EmpiricalEE/uUSB-FP/output/BP1_3D_v240915.jpg

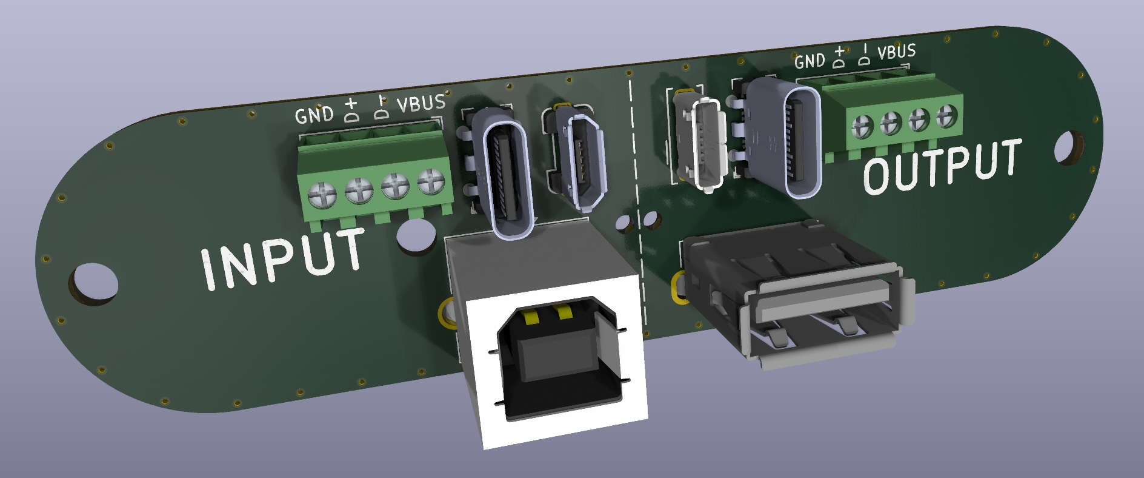
output/BP1_3D_v240915.jpg
